sneakylizard123-4/Overkill-nRF/firmware/Overkill-nRF/src/icon.h

/* ____________________________
   This software is licensed under the MIT License:
   https://github.com/cifertech/nrfbox
   ________________________________________ */

#include <stdint.h>
#include <Arduino.h>


// 'satelite', 16x16px
const unsigned char bitmap_icon_satelite [] PROGMEM = {
  0x00, 0x00, 0x80, 0x00, 0xc0, 0x00, 0xc0, 0x01, 0xe0, 0x31, 0xe0, 0x3b, 0xe0, 0x03, 0xc0, 0x07, 
  0xc0, 0x07, 0x80, 0x0f, 0x00, 0x0f, 0x40, 0x1c, 0xe0, 0x00, 0xf0, 0x07, 0xf0, 0x07, 0x00, 0x00
};

// 'character', 16x16px
const unsigned char bitmap_icon_character [] PROGMEM = {
  0xc0, 0x03, 0xe0, 0x07, 0xa0, 0x05, 0xa0, 0x05, 0xe0, 0x07, 0xe0, 0x07, 0xc0, 0x03, 0x00, 0x00, 
  0x80, 0x01, 0xf0, 0x0f, 0xfc, 0x3f, 0xfe, 0x7f, 0xfe, 0x7f, 0xff, 0xff, 0xf7, 0xef, 0xf7, 0xef
};

// 'save', 16x16px
const unsigned char bitmap_icon_save [] PROGMEM = {
  0xf6, 0x6f, 0xf7, 0xe9, 0xf7, 0xe9, 0xf7, 0xa9, 0xf7, 0xef, 0x0f, 0xf0, 0xff, 0xff, 0x03, 0xc0, 
  0xfb, 0xdf, 0x0b, 0xd0, 0xfb, 0xdf, 0x0b, 0xd0, 0xfb, 0xdf, 0x03, 0xc0, 0xff, 0xff, 0xfe, 0x7f
};

// 'brain', 16x16px
const unsigned char bitmap_icon_brain [] PROGMEM = {
  0x70, 0x0e, 0xf8, 0x1e, 0x9c, 0x3e, 0x7c, 0x3e, 0xf0, 0x3e, 0xee, 0x7e, 0xff, 0xf2, 0xff, 0xec, 
  0xe7, 0xfe, 0xdf, 0xfe, 0x9e, 0x7e, 0x6c, 0x0e, 0xfc, 0x36, 0xfc, 0x1e, 0xf8, 0x1e, 0x70, 0x0e
};

// 'graph', 16x16px
const unsigned char bitmap_icon_graph [] PROGMEM = {
  0x00, 0x00, 0x00, 0x00, 0x22, 0x00, 0x22, 0x00, 0x22, 0x00, 0x22, 0x02, 0x2a, 0x22, 0x2a, 0x22, 
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
  0x00, 0x00, 0x00, 0x00, 0x00, 0x1c, 0x8f, 0x87, 0xc3, 0xe3, 0x71, 0x00, 0x00, 0x00, 0x00, 0x00, 
  0x00, 0x00, 0x00, 0x00, 0x00, 0x1c, 0x0e, 0x83, 0x83, 0xe1, 0x70, 0x00, 0x00, 0x00, 0x00, 0x00, 
  0x00, 0x00, 0x00, 0x00, 0x00, 0x38, 0x1e, 0x80, 0x03, 0xf0, 0x38, 0x00, 0x00, 0x00, 0x00, 0x00, 
  0x00, 0x00, 0x00, 0x00, 0x00, 0x38, 0x3c, 0x80, 0x03, 0x78, 0x38, 0x00, 0x00, 0x00, 0x00, 0x00, 
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
};
